gpyrgiot-code/BackGammonClockScore/7segment48pt7b_numbers.h

#ifndef SEVENSEGMENT48PT7B_NUMBERS_H
#define SEVENSEGMENT48PT7B_NUMBERS_H

const uint8_t SevenSegment48pt7bNumbersBitmaps[] PROGMEM = {
  0x00, 0x3F, 0xFF, 0xFF, 0xC0, 0x00, 0xFF, 0xFF, 0xFF, 0x98, 0x01, 0xFF,
  0xFF, 0xFF, 0xBC, 0x04, 0x7F, 0xFF, 0xFF, 0x3E, 0x06, 0x3F, 0xFF, 0xFF,
  0x3E, 0x07, 0x3F, 0xFF, 0xFE, 0x7F, 0x0F, 0x9F, 0xFF, 0xFE, 0x7F, 0x0F,
  0xCF, 0xFF, 0xFE, 0xFF, 0x0F, 0xE7, 0xFF, 0xFC, 0xFF, 0x0F, 0xF0, 0x00,
  0x01, 0xFF, 0x0F, 0xF0, 0x00, 0x01, 0xFF, 0x0F, 0xF0, 0x00, 0x01, 0xFF,
  0x1F, 0xF0, 0x00, 0x01, 0xFF, 0x1F, 0xF0, 0x00, 0x01, 0xFF, 0x1F, 0xF0,
  0x00, 0x01, 0xFF, 0x1F, 0xF0, 0x00, 0x01, 0xFF, 0x1F, 0xF0, 0x00, 0x01,
  0xFF, 0x1F, 0xF0, 0x00, 0x01, 0xFF, 0x1F, 0xF0, 0x00, 0x01, 0xFE, 0x1F,
  0xF0, 0x00, 0x01, 0xFE, 0x1F, 0xF0, 0x00, 0x01, 0xFE, 0x1F, 0xF0, 0x00,
  0x03, 0xFE, 0x1F, 0xF0, 0x00, 0x03, 0xFE, 0x1F, 0xF0, 0x00, 0x03, 0xFE,
  0x1F, 0xF0, 0x00, 0x03, 0xFE, 0x1F, 0xE0, 0x00, 0x03, 0xFE, 0x1F, 0xE0,
  0x00, 0x03, 0xFE, 0x1F, 0xE0, 0x00, 0x03, 0xFE, 0x3F, 0xE0, 0x00, 0x03,
  0xFE, 0x3F, 0xE0, 0x00, 0x03, 0xFE, 0x3F, 0xC0, 0x00, 0x01, 0xFE, 0x3F,
  0x80, 0x00, 0x00, 0xFE, 0x1F, 0x00, 0x00, 0x00, 0x7C, 0x0C, 0x00, 0x00,
  0x00, 0x38, 0x00, 0x00, 0x00, 0x00, 0x00, 0x00, 0x00, 0x00, 0x00, 0x00,
  0x00, 0x00, 0x00, 0x00, 0x00, 0x0C, 0x00, 0x00, 0x00, 0x30, 0x3E, 0x00,
  0x00, 0x00, 0x7C, 0x3F, 0x00, 0x00, 0x01, 0xFC, 0x3F, 0xC0, 0x00, 0x03,
  0xFC, 0x3F, 0xE0, 0x00, 0x07, 0xFC, 0x3F, 0xC0, 0x00, 0x07, 0xFC, 0x7F,
  0xC0, 0x00, 0x07, 0xFC, 0x7F, 0xC0, 0x00, 0x07, 0xFC, 0x7F, 0xC0, 0x00,
  0x07, 0xFC, 0x7F, 0xC0, 0x00, 0x07, 0xFC, 0x7F, 0xC0, 0x00, 0x07, 0xFC,
  0x7F, 0xC0, 0x00, 0x07, 0xFC, 0x7F, 0xC0, 0x00, 0x07, 0xFC, 0x7F, 0xC0,
  0x00, 0x07, 0xF8, 0x7F, 0xC0, 0x00, 0x07, 0xF8, 0x7F, 0xC0, 0x00, 0x0F,
  0xF8, 0x7F, 0xC0, 0x00, 0x0F, 0xF8, 0x7F, 0xC0, 0x00, 0x0F, 0xF8, 0x7F,
  0xC0, 0x00, 0x0F, 0xF8, 0x7F, 0xC0, 0x00, 0x0F, 0xF8, 0x7F, 0x80, 0x00,
  0x0F, 0xF8, 0x7F, 0x80, 0x00, 0x0F, 0xF8, 0x7F, 0x80, 0x00, 0x0F, 0xF8,
  0xFF, 0x80, 0x00, 0x0F, 0xF8, 0xFF, 0x80, 0x00, 0x0F, 0xF8, 0xFF, 0x3F,
  0xFF, 0xEF, 0xF8, 0xFE, 0x7F, 0xFF, 0xE7, 0xF8, 0xF8, 0xFF, 0xFF, 0xE7,
  0xF0, 0x71, 0xFF, 0xFF, 0xF7, 0xF0, 0x63, 0xFF, 0xFF, 0xF3, 0xF0, 0x47,
  0xFF, 0xFF, 0xF3, 0xE0, 0x0F, 0xFF, 0xFF, 0xF3, 0xC0, 0x1F, 0xFF, 0xFF,
  0xF9, 0x80, 0x03, 0xFF, 0xFF, 0xF8, 0x00, 0x01, 0x80, 0x3C, 0x03, 0xE0,
  0x3E, 0x07, 0xF0, 0x7F, 0x0F, 0xF0, 0xFF, 0x1F, 0xF1, 0xFF, 0x1F, 0xF1,
  0xFF, 0x1F, 0xF1, 0xFF, 0x1F, 0xF1, 0xFF, 0x1F, 0xF1, 0xFE, 0x1F, 0xE1,
  0xFE, 0x3F, 0xE3, 0xFE, 0x3F, 0xE3, 0xFE, 0x3F, 0xE3, 0xFE, 0x3F, 0xE3,
  0xFE, 0x3F, 0xE1, 0xFE, 0x0F, 0xE0, 0x7C, 0x03, 0x80, 0x00, 0x00, 0x00,
  0x00, 0x03, 0x00, 0x7C, 0x1F, 0xC3, 0xFC, 0x7F, 0xC7, 0xFC, 0x7F, 0xC7,
  0xFC, 0x7F, 0xC7, 0xFC, 0x7F, 0xC7, 0xFC, 0x7F, 0xC7, 0xF8, 0x7F, 0x8F,
  0xF8, 0xFF, 0x8F, 0xF8, 0xFF, 0x8F, 0xF8, 0xFF, 0x8F, 0xF8, 0xFF, 0x8F,
  0xF8, 0xFF, 0x8F, 0xF8, 0x7F, 0x87, 0xF0, 0x7F, 0x03, 0xF0, 0x3E, 0x03,
  0xC0, 0x18, 0x00, 0x00, 0x3F, 0xFF, 0xFF, 0xC0, 0x00, 0xFF, 0xFF, 0xFF,
  0x98, 0x01, 0xFF, 0xFF, 0xFF, 0xBC, 0x00, 0x7F, 0xFF, 0xFF, 0x3E, 0x00,
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
};

const GFXglyph SevenSegment48pt7bNumbersGlyphs[] PROGMEM = {
  {    0, 40, 71, 44,   4,  -70 }, // 0
  {  355, 12, 69, 44,  32,  -69 }, // 1
  {  459, 40, 71, 44,   4,  -70 }, // 2
  {  814, 37, 71, 44,   7,  -70 }, // 3
  { 1143, 38, 69, 44,   6,  -69 }, // 4
  { 1471, 36, 71, 44,   6,  -70 }, // 5
  { 1791, 38, 71, 44,   4,  -70 }, // 6
  { 2129, 33, 70, 44,  11,  -70 }, // 7
  { 2418, 40, 71, 44,   4,  -70 }, // 8
  { 2773, 38, 71, 44,   6,  -70 }, // 9
  { 3111, 12, 40, 17,   4,  -54 } // :
};

const GFXfont SevenSegment48pt7bNumbers PROGMEM = {
  (uint8_t *)SevenSegment48pt7bNumbersBitmaps,
  (GFXglyph *)SevenSegment48pt7bNumbersGlyphs,
  0x30, 0x3A, 97
};

#endif
