gpyrgiot-code/BackGammonClockScore/FreeSansBold48pt7b_numbers.h

#ifndef FREESANSBOLD48PT7B_NUMBERS_H
#define FREESANSBOLD48PT7B_NUMBERS_H

const uint8_t FreeSansBold48pt7bNumbersBitmaps[] PROGMEM = {
  0x00, 0x00, 0x7F, 0xF0, 0x00, 0x00, 0x00, 0x0F, 0xFF, 0xF8, 0x00, 0x00,
  0x00, 0xFF, 0xFF, 0xF8, 0x00, 0x00, 0x0F, 0xFF, 0xFF, 0xF8, 0x00, 0x00,
  0x7F, 0xFF, 0xFF, 0xF0, 0x00, 0x03, 0xFF, 0xFF, 0xFF, 0xE0, 0x00, 0x1F,
  0xFF, 0xFF, 0xFF, 0xC0, 0x00, 0xFF, 0xFF, 0xFF, 0xFF, 0x80, 0x07, 0xFF,
  0xFF, 0xFF, 0xFF, 0x00, 0x1F, 0xFF, 0xFF, 0xFF, 0xFE, 0x00, 0xFF, 0xFF,
  0xFF, 0xFF, 0xF8, 0x03, 0xFF, 0xF8, 0x0F, 0xFF, 0xF0, 0x1F, 0xFF, 0x80,
  0x0F, 0xFF, 0xC0, 0x7F, 0xFC, 0x00, 0x1F, 0xFF, 0x83, 0xFF, 0xF0, 0x00,
  0x3F, 0xFE, 0x0F, 0xFF, 0x80, 0x00, 0xFF, 0xF8, 0x3F, 0xFE, 0x00, 0x01,
  0xFF, 0xF1, 0xFF, 0xF0, 0x00, 0x07, 0xFF, 0xC7, 0xFF, 0xC0, 0x00, 0x1F,
  0xFF, 0x1F, 0xFF, 0x00, 0x00, 0x7F, 0xFC, 0x7F, 0xFC, 0x00, 0x00, 0xFF,
  0xF1, 0xFF, 0xF0, 0x00, 0x03, 0xFF, 0xEF, 0xFF, 0x80, 0x00, 0x0F, 0xFF,
  0xBF, 0xFE, 0x00, 0x00, 0x3F, 0xFE, 0xFF, 0xF8, 0x00, 0x00, 0xFF, 0xFB,
  0xFF, 0xE0, 0x00, 0x03, 0xFF, 0xEF, 0xFF, 0x80, 0x00, 0x0F, 0xFF, 0xBF,
  0xFE, 0x00, 0x00, 0x3F, 0xFE, 0xFF, 0xF8, 0x00, 0x00, 0xFF, 0xFB, 0xFF,
  0xE0, 0x00, 0x03, 0xFF, 0xEF, 0xFF, 0x80, 0x00, 0x0F, 0xFF, 0xBF, 0xFE,
  0x00, 0x00, 0x3F, 0xFF, 0xFF, 0xF8, 0x00, 0x00, 0xFF, 0xFF, 0xFF, 0xE0,
  0x00, 0x03, 0xFF, 0xFF, 0xFF, 0x80, 0x00, 0x0F, 0xFF, 0xFF, 0xFE, 0x00,
  0x00, 0x3F, 0xFF, 0xFF, 0xF8, 0x00, 0x00, 0xFF, 0xFF, 0xFF, 0xE0, 0x00,
  0x03, 0xFF, 0xFF, 0xFF, 0x80, 0x00, 0x0F, 0xFF, 0xFF, 0xFE, 0x00, 0x00,
  0x3F, 0xFF, 0xFF, 0xF8, 0x00, 0x00, 0xFF, 0xFB, 0xFF, 0xE0, 0x00, 0x03,
  0xFF, 0xEF, 0xFF, 0x80, 0x00, 0x0F, 0xFF, 0xBF, 0xFE, 0x00, 0x00, 0x3F,
  0xFE, 0xFF, 0xF8, 0x00, 0x00, 0xFF, 0xFB, 0xFF, 0xE0, 0x00, 0x03, 0xFF,
  0xEF, 0xFF, 0x80, 0x00, 0x0F, 0xFF, 0xBF, 0xFE, 0x00, 0x00, 0x3F, 0xFE,
  0x7F, 0xFC, 0x00, 0x00, 0xFF, 0xF9, 0xFF, 0xF0, 0x00, 0x03, 0xFF, 0xC7,
  0xFF, 0xC0, 0x00, 0x1F, 0xFF, 0x1F, 0xFF, 0x00, 0x00, 0x7F, 0xFC, 0x7F,
  0xFC, 0x00, 0x01, 0xFF, 0xF0, 0xFF, 0xF8, 0x00, 0x0F, 0xFF, 0xC3, 0xFF,
  0xE0, 0x00, 0x3F, 0xFE, 0x0F, 0xFF, 0xC0, 0x01, 0xFF, 0xF8, 0x1F, 0xFF,
  0x80, 0x0F, 0xFF, 0xE0, 0x7F, 0xFF, 0x00, 0x7F, 0xFF, 0x01, 0xFF, 0xFF,
  0x07, 0xFF, 0xFC, 0x03, 0xFF, 0xFF, 0xFF, 0xFF, 0xE0, 0x07, 0xFF, 0xFF,
  0xFF, 0xFF, 0x80, 0x1F, 0xFF, 0xFF, 0xFF, 0xFC, 0x00, 0x3F, 0xFF, 0xFF,
  0xFF, 0xE0, 0x00, 0x7F, 0xFF, 0xFF, 0xFF, 0x00, 0x00, 0xFF, 0xFF, 0xFF,
  0xF8, 0x00, 0x01, 0xFF, 0xFF, 0xFF, 0xC0, 0x00, 0x03, 0xFF, 0xFF, 0xFE,
  0x00, 0x00, 0x03, 0xFF, 0xFF, 0xE0, 0x00, 0x00, 0x03, 0xFF, 0xFF, 0x00,
  0x00, 0x00, 0x01, 0xFF, 0xE0, 0x00, 0x00, 0x00, 0x00, 0x07, 0xFC, 0x00,
  0x00, 0x3F, 0xF0, 0x00, 0x00, 0xFF, 0xC0, 0x00, 0x03, 0xFF, 0x00, 0x00,
  0x1F, 0xFC, 0x00, 0x00, 0xFF, 0xF0, 0x00, 0x03, 0xFF, 0xC0, 0x00, 0x1F,
  0xFF, 0x00, 0x01, 0xFF, 0xFC, 0x00, 0x0F, 0xFF, 0xF0, 0x00, 0xFF, 0xFF,
  0xC0, 0x3F, 0xFF, 0xFF, 0xFF, 0xFF, 0xFF, 0xFF, 0xFF, 0xFF, 0xFF, 0xFF,
  0xFF, 0xFF, 0xFF, 0xFF, 0xFF, 0xFF, 0xFF, 0xFF, 0xFF, 0xFF, 0xFF, 0xFF,
  0xFF, 0xFF, 0xFF, 0xFF, 0xFF, 0xFF, 0xFF, 0xFF, 0xFF, 0xFF, 0xFF, 0xFF,
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
};

const GFXglyph FreeSansBold48pt7bNumbersGlyphs[] PROGMEM = {
  {    0, 46, 70, 52,   3,  -67 }, // 0
  {  403, 30, 67, 52,   6,  -66 }, // 1
  {  655, 45, 68, 52,   3,  -67 }, // 2
  { 1038, 46, 70, 52,   3,  -67 }, // 3
  { 1441, 47, 67, 52,   2,  -66 }, // 4
  { 1835, 46, 69, 52,   3,  -66 }, // 5
  { 2232, 46, 70, 52,   3,  -67 }, // 6
  { 2635, 47, 67, 52,   3,  -66 }, // 7
  { 3029, 47, 70, 52,   2,  -67 }, // 8
  { 3441, 46, 70, 52,   3,  -67 } // 9
};

const GFXfont FreeSansBold48pt7bNumbers PROGMEM = {
  (uint8_t *)FreeSansBold48pt7bNumbersBitmaps,
  (GFXglyph *)FreeSansBold48pt7bNumbersGlyphs,
  0x30, 0x39, 151
};

#endif
